Nullkraft/3GHz-Spectrum-Analyzer/CmdProcessor/include/SpecAnn.h

#ifndef _SPECANN_
#define _SPECANN_

#include "adf4356.h"  // driver
#include "max2871.h"  // driver
#include <SPI.h>

/* Vref = 2.595  Volts/ADC_bit == 0.002536 Volts
 * Noise-floor ≈ 0.488 Volts
 * ADC_value of 193 ≈ 0.488/0.002536
*/

class SpecificInstruction {
  private:
    uint16_t data;  // 16 bits
    byte cmd;
    byte addr;
    const byte addrMask = 0x07;  // Mask out 3 bits of 'Register Address' from serialWord[1]
    const byte cmdMask = 0x1F;      // Mask out the upper 5-bits for cmd
    /* All the values required by the spi_write() command */
    uint32_t regWord;    // Holds the register contents to be written to the selected device

  public:
    SpecificInstruction() : data(0), cmd(0), addr(0), regWord(0) {}
/*           Serial Word with Command Flag:
      ________________________________________________
    /________________________________________________/|
   |       Embedded      | Instr- |Addr.|  Command  | | NOTE: Command Flag
   |       Data          | uction |     |   Flag    | |        always = 0xFF
   |---------------------+--------+-----+-----------| |
   | xxxx_xxxx_xxxx_xxxx | xxxx_x | xxx | 1111_1111 | |
   |________________________________________________|/
*/
    void parseSpecificInstruction(uint32_t serialWord) {
      uint8_t newAddr = (serialWord >> 8) & addrMask;   // Mask out the lsb 3-bit Address
      if ((newAddr <= 4) || (newAddr == 7)) { // Reserves addresses 5 and 6
      // if ((newAddr <= 4)) { // Use this 'if statement' for testing 'Invalid Address' error
        addr = newAddr;
        cmd = (serialWord >> 11) & cmdMask;
        data = serialWord >> 16;            // Shift the upper 16-bits down into data
      } else {
        Serial.print("Invalid Address, <");
        Serial.print(newAddr);
        Serial.print(">, found in Specific Instruction <");
        Serial.print(serialWord);
        Serial.print(">");
      }
    }

    uint16_t getData() const { return data; }
    uint16_t getCommand() const { return cmd; }
    uint16_t getAddress() const { return addr; }
};


// General LO Instructions
class GeneralInstruction {
  // 
};


class SpecAnn {
  private:
    #define NUM_MISC_FUNCTIONS 4
    #define NUM_CLK_FUNCTIONS 3
    /* All the values required by the spi_write() command */
    uint32_t regWord;    // Holds the register contents to be written to the selected device

  public:
    static uint8_t select_pin;  // Chip selected for programming
    uint8_t adc_pin = 99;       // Intialize to an invalid pin

    /* Command-to-Function Mapping:
    
     Each instruction found in the API ('Instruction List XXX.ods') has an
     associated Address and Command. The Address identifies the component
     and the Command identifies the action to be performed.
    
     The 'Command Number' is found in the API document and is 5 bits long.
     It is ideal as an index into one of the xxxYYYYCmnMap[] arrays. The
     CmdMap arrays decouple the API Command Number from the layout of the
     function-pointer arrays found in the max2871.h and adf4356.h files.
    
     The enums provide descriptive command names for the function-pointer
     arrays instead of using the Command Numbers.
    
     For a list of available commands and their corresponding functions, refer
     to the Execute() function in max2871.h and the Execute() function in adf4356.h.
    */
    enum loCmdList{GERERAL, RFOFF, N4DBM, N1DBM, P2DBM, P5DBM, CHANGE_FREQ, TRI, DLD, DIV_MODE, NA=30, };
    enum arduinoCmdList{LED_OFF, LED_ON, VERSION, BEGIN_SWEEP, };
    enum ckCmdLIst{ALL_OFF, REF_LO_ON, REF_HI_ON, };

    // Command map declarations
    uint8_t max2871CmdMap[10] {
      SpecAnn::NA, SpecAnn::RFOFF, SpecAnn::N4DBM, SpecAnn::N1DBM, SpecAnn::P2DBM,
      SpecAnn::P5DBM, SpecAnn::NA, SpecAnn::TRI, SpecAnn::DLD, SpecAnn::DIV_MODE
      };
    uint8_t adf4356CmdMap[9] {
      SpecAnn::NA, SpecAnn::RFOFF, SpecAnn::N4DBM, SpecAnn::N1DBM, SpecAnn::P2DBM,
      SpecAnn::P5DBM, SpecAnn::NA, SpecAnn::TRI, SpecAnn::DLD
      };
    uint8_t arduinoCmdMap[4] {
      SpecAnn::LED_OFF, SpecAnn::LED_ON, SpecAnn::VERSION, SpecAnn::BEGIN_SWEEP
      };
    uint8_t clkCmdMap[3] {
      SpecAnn::ALL_OFF, SpecAnn::REF_LO_ON, SpecAnn::REF_HI_ON
      };

    ADF4356_LO LO1;
    ADF4356_LO* ptrLO1 = &LO1;
    MAX2871_LO LO2;
    MAX2871_LO* ptrLO2 = &LO2;
    MAX2871_LO LO3;
    MAX2871_LO* ptrLO3 = &LO3;
    MAX2871_LO* LO = ptrLO3;

    // Status codes use the 4 msbits of the 16 bit ADC return values
    // const int start_noise_floor = 0xD0;  // First in the series of ADC noise-floor readings
    // const int end_noise_floor   = 0xE0;  // Last in the series of ADC noise-floor readings
    static constexpr int failedToLock = 0xF000;   // VCO Failed to lock message
    static constexpr int rleCountPacket = 0xE000; // Data contains Run Line Encoding (RLE) count
    static constexpr uint16_t rleIncremented = 0xD000; // RLE count was incremented - No action required (Internal use only)

    static constexpr uint16_t ATTEN_Data_Mask = 0x7F;  // 7 bit mask for programming the Attenuator

    /*********** ARDUINO PIN DEFINITIONS ***********/
    static constexpr uint8_t LO1_SEL = A3;
    static constexpr uint8_t LO2_SEL = 3;
    static constexpr uint8_t LO3_SEL = A4;
    static constexpr uint8_t REF_LO_SEL = 8;
    static constexpr uint8_t REF_HI_SEL = 9;
    static constexpr uint8_t ADC_SEL_045 = A0;  // ADC for LO2
    static constexpr uint8_t ADC_SEL_315 = A1;  // ADC for LO3
    static constexpr uint8_t PLL_MUX = A2;      // Equals physical pin 16 on Port C (use PCMSK1)
    static constexpr uint8_t ATTEN_SEL = A5;
    //static constexpr uint8_t SPI_MOSI  = 11;   // Reserved by the SPI Library
    //static constexpr uint8_t SPI_MISO  = 12;   // Reserved by the SPI Library
    //static constexpr uint8_t SPI_CLOCK = 13;   // Reserved by the SPI Library

    // Command Word Addresses of all the hardware Integrated Circuit chips
    // TODO: Create the list in a config file that remains with the project files.
    static constexpr uint8_t Attenuator = 0;
    static constexpr uint8_t LO1_addr = 1;
    static constexpr uint8_t LO2_addr = 2;
    static constexpr uint8_t LO3_addr = 3;
    static constexpr uint8_t RefClock = 4;
    static constexpr uint8_t MISC_addr = 7;

    ///////// Move to SpecAnn.h /////////
    unsigned long start_PLL_Lock_time;
    const unsigned long int PLL_Lock_timeout = 500; // usec. Use 195 for testing some failures to lock.
    int LOCKED;
    // Declare external RLE count variable
    uint16_t rleCount;
    volatile uint16_t a2dAmplitude;
    uint8_t* ampl_byte = (uint8_t*)&a2dAmplitude;
    // uint8_t adc_pin;
    /////////////////////////////////////
    uint8_t hi_byte;
    uint8_t lo_byte;
    
    bool DEBUG = false;

    /*********** HARDWARE DEFINITIONS END *******/
    SpecAnn();  //Ctor
    void init_specann();
    void builtinLEDOff();
    void builtinLEDOn();
    void version();
    void end_sweep_ack();

    void all_ref_off();
    void ref_LO();
    void ref_HI();

    void updateLORegisters(MAX2871_LO* loPtr, uint8_t selectPin, uint8_t command, uint32_t serialWord);
    void updateAtten(uint8_t reg, uint8_t selectPin);

    typedef void (SpecAnn::*MiscFuncs)();
    void miscExecute(uint8_t);
    void selectHW(uint16_t Data16, byte cmdIdx, byte Address, uint32_t serialWord);
    uint16_t programHW(uint32_t serialWord);

    // Array of function-pointers containing the
    // 'Spectrum Analyzer miscellenious functions'
    MiscFuncs miscCmds[NUM_MISC_FUNCTIONS] = {
      &SpecAnn::builtinLEDOff, // Command idx 0
      &SpecAnn::builtinLEDOn,  // Command idx 1
      &SpecAnn::version,       // Command idx 2
      &SpecAnn::end_sweep_ack, // Command idx 3
    };

    typedef void (SpecAnn::*RefClockFuncs)();
    void clkExecute(uint8_t);

    // function-pointer array for clock selection functions
    RefClockFuncs refClockCmds[NUM_CLK_FUNCTIONS] = {
      &SpecAnn::all_ref_off,  // Command number 0
      &SpecAnn::ref_LO,       // Command number 1
      &SpecAnn::ref_HI,       // Command number 2
    };


};

#endif  // _SPECANN_
