Nullkraft/3GHz-Spectrum-Analyzer/CmdProcessor/src/SpecAnn.cpp

#include "SpecAnn.h"

uint8_t SpecAnn::select_pin = 255;

SpecAnn::SpecAnn() {
  // lo.begin(SpecAnn::LO2_SEL);
  ref_LO();
  // Presets for LO3
  LO3.Curr.Reg[0] = 0x002081C8;  // LO3 = 270 MHz with 66 MHz ref clock
  LO3.Curr.Reg[1] = 0x400103E9;
  LO3.Curr.Reg[2] = 0x98005F42;  // Digital Lock Detect ON
  LO3.Curr.Reg[3] = 0x00001F23;
  LO3.Curr.Reg[4] = 0x63CE803C;
  LO3.Curr.Reg[5] = 0x00400005;
  LO3.Curr.Reg[6] = 0x80005F42;  // Digital Lock Detect ON
}

/* Starting with one of the MAX2871 chips makes initializing LO1 much more consistent. Why?
   Initialize IC's LO1, LO2 and LO3 by programming them twice IAW manufacturer's specsheet
*/
void SpecAnn::init_specann() {
  LO1.begin(LO1_SEL);
  LO2.begin(LO2_SEL);
  LO3.begin(LO3_SEL);
  delay(20);
  LO1.begin(LO1_SEL);
  LO2.begin(LO2_SEL);
  LO3.begin(LO3_SEL);
}

void SpecAnn::updateLORegisters(MAX2871_LO* LoPtr, uint8_t selectPin, uint8_t command, uint32_t serialWord) {
  LO = LoPtr;
  SpecAnn::select_pin = selectPin;  // Update global static select_pin to selected chip
  uint32_t regWord = LO->Execute(max2871CmdMap[command], serialWord);
  LO->update(regWord, SpecAnn::select_pin);
}

// Program the Digital Attenuator by sending and latching a single byte
void SpecAnn::updateAtten(uint8_t level, uint8_t selectPin) {
  SpecAnn::select_pin = selectPin;  // Update global static select_pin to selected chip
  level = level & ATTEN_Data_Mask;
  SPI.beginTransaction(SPISettings(16000000, LSBFIRST, SPI_MODE0));
  SPI.begin();
  SPI.transfer(level);
  digitalWrite(SpecAnn::select_pin, HIGH);
  digitalWrite(SpecAnn::select_pin, LOW);
  SPI.end();
}

void SpecAnn::builtinLEDOn() {
  digitalWrite(LED_BUILTIN, HIGH);
  Serial.print(F("Called builtin_LED_On"));
}

void SpecAnn::builtinLEDOff() {
  digitalWrite(LED_BUILTIN, LOW);
  Serial.print(F("Called builtin_LED_Off"));
}

void SpecAnn::version() {
  Serial.print(F("- WN2A Spectrum Analyzer CmdProcessor Oct. 2023"));
}

// Send the end-of-sweep acknowledgement back to the controller
void SpecAnn::end_sweep_ack() {
  Serial.write(0xFF);
  Serial.write(0xFF);
}

// Turn both ref_clocks off
void SpecAnn::all_ref_off() {
  digitalWrite(REF_LO_SEL, LOW);
  digitalWrite(REF_HI_SEL, LOW);
}
// Turn on low freq reference clock, Ref1, and turn off high freq reference clock, Ref2
void SpecAnn::ref_LO() {
  digitalWrite(REF_LO_SEL, HIGH);
  digitalWrite(REF_HI_SEL, LOW);
}
// Turn on high freq reference clock, Ref2, and turn off low freq reference clock, Ref1
void SpecAnn::ref_HI() {
  digitalWrite(REF_LO_SEL, LOW);
  digitalWrite(REF_HI_SEL, HIGH);
}

void SpecAnn::clkExecute(uint8_t commandIndex) {
  if (commandIndex < NUM_CLK_FUNCTIONS) {
    (this->*refClockCmds[commandIndex])();
  }
}

// Select the miscCmds function to be executed
void SpecAnn::miscExecute(uint8_t commandIndex) {
  if (commandIndex < NUM_MISC_FUNCTIONS) {
    // Call the function 
    (this->*miscCmds[commandIndex])();
  }
}

void SpecAnn::selectHW(uint16_t Data16, byte cmdIdx, byte Address, uint32_t serialWord) {
  switch (Address) {
    case Attenuator:
      updateAtten(static_cast<uint8_t>(Data16), ATTEN_SEL);
      break;
    case LO1_addr:
      select_pin = LO1_SEL;
      LO1.set_N_bits(Data16);                           // Set the new INT_N bits into Register 0
      regWord = LO1.Execute(adf4356CmdMap[cmdIdx], 0);  // This selects from 1 of 7 adf4356 commands
      LO1.update(regWord, select_pin);                  // Write Reg[4] for set_TRI/set_DLD, ELSE Reg[6]
      LO1.update(LO1.Curr.Reg[0], select_pin);          // followed by Reg[0] (REQUIRED by specsheet)
      break;
    case LO2_addr:
      adc_pin = ADC_SEL_315;  // Select the ADC that reads the output of the LO2 RF path
      select_pin = LO2_SEL;   // ALWAYS keep track of the currently selected chip
      updateLORegisters(ptrLO2, select_pin, cmdIdx, serialWord);
      break;
    case LO3_addr:
      adc_pin = ADC_SEL_045;  // Select the ADC that reads the output of the LO3 RF path
      select_pin = LO3_SEL;   // ALWAYS keep track of the currently selected chip
      updateLORegisters(ptrLO3, select_pin, cmdIdx, serialWord);
      break;
    case RefClock:
      clkExecute(cmdIdx);
      break;
    case MISC_addr:
      miscExecute(arduinoCmdMap[cmdIdx]);
      break;
    default:
      Serial.print(F("Requested Address:"));
      Serial.print(Address);
      Serial.println(F(" not found"));
  }   /* End switch(Address) */
}

uint16_t SpecAnn::programHW(uint32_t serialWord) {
    // M:  Set R[1], bits[14:3] to program the new value for M
    LO->set_M_bits(serialWord);
    // N & F:  Set bits R[0], bits[22:15] for new N, and R[0], bits[14:3] for new F
    LO->set_NF_bits(serialWord);
    // Program the selected LO starting with the higher numbered registers first
    LO->update(LO->Curr.Reg[1], select_pin);
    LO->update(LO->Curr.Reg[0], select_pin);

    // Wait for selected LO2 or LO3 to Lock
    start_PLL_Lock_time = micros();
    uint16_t thresholdValue = 0x100;  // Example threshold value, set accordingly

    while (true) {
        LOCKED = digitalRead(PLL_MUX);  // Check the mux pin to see if we get a lock
        analogRead(adc_pin);  // HACK to prime the ADC. Fix the ADC input impedance?
        // We either get a lock or we check for a timeout.
        if (LOCKED) {
            a2dAmplitude = analogRead(adc_pin);
            break;
        }
        // Trigger the timeout if we don't get a lock. We still want the amplitude
        // data so a 'failure to lock' message (failedToLock) is OR'd with the data so that the
        // user is notified that the amplitude may not be exact.
        if ((micros() - start_PLL_Lock_time) > PLL_Lock_timeout) {
            a2dAmplitude = analogRead(adc_pin);
            a2dAmplitude |= failedToLock;  // Send failure report to PC
            break;
        }
        // Bypass the lock detect when debugging the Arduino by itself.
        if (DEBUG) {
            delayMicroseconds(100);
            break;
        }
    }

    // Amplitude is less than the threshold
    if (a2dAmplitude < thresholdValue) {
        // Increment the (parent) relCount for consecutive values below the threshold
        rleCount++;
        if (rleCount == 0xFFF) {  // Max count for 12 bits
            // Encode the count then reset
            a2dAmplitude = rleCountPacket | rleCount;
            rleCount = 0;
        } else {
            // Middle of an RLE run? Return 'RLE Incremented' message only (no data)
            a2dAmplitude = rleIncremented;
        }
    }

    // Any non-zero a2dAmplitude value will cause the calling program to send
    // the RLE-count first followed by the contents of this a2dAmplitude value.
    return a2dAmplitude;
}
