Nullkraft/3GHz-Spectrum-Analyzer/CmdProcessor/include/max2871.h

#ifndef _MAX2871_
#define _MAX2871_

#include <SPI.h>

class MAX2871_LO {
  typedef struct maxRegisters {
    static constexpr byte numRegisters = 7;
    uint32_t Reg[numRegisters] = {0x001D47B0,  // R[0] N = Bits[30:15], F = Bits[14:3]
                                  0x40017FE1,  // R[1] M = Bits[14:3]
                                  0x80005F42,  // R[2] Digital Lock detect OFF
                                  0x04009F23,  // R[3] Fast Lock enabled
                                  0x638E83C4,  // R[4] RFout_B enabled @ +5dBm / RFout_A disabled
                                  0x00400005,  // R[5]
                                  0x98005F42   // R[6] Digital Lock detect ON
                                };
  } max2871Registers;

  private:
    static constexpr int NUMBER_OF_FUNCTIONS = 8;
    // The MAX2871 requires a 20 ms delay only on the first init
    // See the begin() function
    bool first_init;

  public:
    MAX2871_LO() : first_init(true) {  // Ctor initialzes first_init
      // SPI.begin();   // BUG: Causes Arduino LED to stop working
    }
    
    max2871Registers Curr;  // Read/Write copy of the registers

    /* 6 bit mask of Embedded Data from serial Specific Command */
    static constexpr short Data_Mask = 0x3F;

    /* 12 bit mask, R[1] bits [14:3], for Fractional Modulus Value, M */
    #define M_set 0x7FF8      // const uint32_t M_set = 0x7FF8;
    #define M_clr 0xFFFF8007  // const uint32_t M_clr = 0xFFFF8007;

    /* 12 bit mask, R[0] bits [14:3], for Frequency Division Value, F */
    #define F_set 0x7FF8      // const uint32_t F_set = 0x7FF8;
    #define F_clr 0xFFFF8007  // const uint32_t F_clr = 0xFFFF8007;

    /* 8 bit mask, R[0] bits [22:15], for Integer Counter, N */
    #define N_set 0x7F8000    // const uint32_t N_set = 0x7F8000;
    #define N_clr 0xFFFF8007  // const uint32_t N_clr = 0xFFFF8007;

    /* 20 bit mask, R[0] bits [22:3], for N and F */
    #define NF_set 0x7FFFF8   // const uint32_t NF_set = 0x7FFFF8;
    #define NF_clr 0xFF800007 // const uint32_t NF_clr = 0xFF800007;

    /* R4<8> and R4<5> disable RFoutB and RFoutA */
    static constexpr uint32_t RFpower_off = 0xFFFFFE07;

    /* R4<7:6> Adjust the RFoutB power level. (RFoutA is off by default) */
    /* Also provides a differenct name to make the main sketch more readable */
    static constexpr uint32_t Power_Level_Mask = RFpower_off;

    /* R4<7:6> Adjust the RFoutB power level. (RFoutA is off by default) */
    /* The MSbit, R4<8>, ensures that the RFout is enabled */
    static constexpr uint32_t neg4dBm = 0x100;
    static constexpr uint32_t neg1dBm = 0x140;
    static constexpr uint32_t pos2dBm = 0x180;
    static constexpr uint32_t pos5dBm = 0x1C0;

    /* R4<22:20> Set the RFOut Divider Mode to 1, 2, 4, 8, 16, 32, 64, or 128 */
    #define RFOUT_DIV_MASK 0xFF8FFFFF // const uint32_t RFOUT_DIV_MASK = 0xFF8FFFFF;  // 00700000;

    /*****  ----------------------- NOTE: --------------------------  *****/
    /***** | Enabling Tristate, Mux_Set_TRI, automatically disables | *****/
    /***** | Digital Lock Detect, Mux_Set_DLD, and vice versa.      | *****/
    /*****  --------------------------------------------------------  *****/

    /* 'AND' Mux_Set_TRI with R2 to enable Tristate. Affects bits <28:26> */
    static constexpr uint32_t Mux_Set_TRI = 0xE3FFFFFF;

    /* 'OR' Mux_Set_DLD with R2 to enable Digital Lock Detect. Affects bits <28:26> */
    static constexpr uint32_t Mux_Set_DLD = 0x18000000;

    uint32_t spiMaxSpeed = 20000000;   // 20 MHz max SPI clock

    // Create a function pointer to use in the function pointer array
    typedef uint32_t (MAX2871_LO::*CmdFunc)(uint32_t);

    void begin(uint8_t);
    void set_NF_bits(uint32_t);
    void set_M_bits(uint32_t);
    // void setFrequency(float frequency, float ref_clock, uint8_t selectPin);
    // void setFrequency(uint16_t F, uint16_t M, uint8_t N, uint8_t selectPin);
    void FMN_from_freq(float target_freq_MHz, float ref_clock, uint16_t &F, uint16_t &M, uint8_t &N);
    void update(uint32_t reg, uint8_t selectPin); // Write 4 bytes to chip register
    uint32_t Execute(byte commandIndex, uint32_t controlWord);

  private:
    // Create the function pointer array
    CmdFunc maxCmds[NUMBER_OF_FUNCTIONS] = {
      &MAX2871_LO::turn_off_RF,   // 0
      &MAX2871_LO::set_n4dBm,     // 1
      &MAX2871_LO::set_n1dBm,     // 2
      &MAX2871_LO::set_p2dBm,     // 3
      &MAX2871_LO::set_p5dBm,     // 4
      &MAX2871_LO::set_TRI,       // 5
      &MAX2871_LO::set_DLD,       // 6
      &MAX2871_LO::set_DIV_MODE,  // 7
    };

    /* dummyReg sets the function signatures so they all match.
     * If not, then more than one function-pointer-array would
     * be needed, negating the benefit of 'indexing' into the
     * array.
     */
    uint32_t set_DLD(uint32_t);
    uint32_t set_TRI(uint32_t);
    uint32_t turn_off_RF(uint32_t);
    uint32_t set_n4dBm(uint32_t);
    uint32_t set_n1dBm(uint32_t);
    uint32_t set_p2dBm(uint32_t);
    uint32_t set_p5dBm(uint32_t);
    uint32_t set_DIV_MODE(uint32_t reg);
};

#endif
